AdamDubois/OverClock/Code/Codes_RaspPi/Qt/Interface_9avril/README.md

# Projet Bombe - Code/Code_RaspPi/Qt/Interface_9avril

## Architecture de ce dossier
- OverClockUI : suite des fichiers pour la conception de l'interface.
- OverClockUI.zip : Fichier compressé à mettre sur le Raspberry Pi 4.
