AdamDubois/OverClock/Code/Codes_RaspPi/9Avril/Bouton/README.md

# Projet Bombe - Code/Codes_RaspPi/9Avril/Bouton

## Description

Dossier contenant les codes pour l'énigme des boutons. Il contient les codes pour lire les données des boutons connectés aux ESP32 via I2C et pour envoyer des commandes I2C aux ESP32_DEL pour tester les animations de DEL programmables.

## Architecture de ce dossier

Ce dossier contient les fichiers de code pour l'énigme des boutons, notamment pour les interactions entre le Raspberry Pi et les ESP32 du projet Bombe. Il est organisé de la manière suivante :
- `Config.py` : Fichier de configuration pour les codes de l'énigme des boutons. Il contient les adresses I2C des ESP32 utilisés pour les boutons et les ESP32_DEL, ainsi que les commandes I2C à envoyer pour tester les animations de DEL programmables.
- `EnigmeBouton.py` : Code principal pour l'énigme des boutons. Lit les données du ESP-IO et les traites pour vérifier si elles correspondent à la solution de l'énigme. Affiche les résultats dans la console et envoie des commandes I2C au ESP32_DEL pour tester les animations de DEL programmables en fonction des données reçues.
- `I2C_handler.py` : Fichier de code pour la gestion des communications I2C entre le Raspberry Pi et les ESP32 du projet Bombe. Contient des fonctions pour envoyer des commandes I2C aux ESP32_DEL et pour lire les données des ESP-IO.
- `Log.py` : Fichier de code pour la gestion des logs à afficher dans le terminal pour l'énigme des boutons.
