AdamDubois/OverClock/Code/Codes_RaspPi/Enigmes/1/README.md

# Projet Bombe - Code/Codes_RaspPi/Enigmes/1

## Description

Dossier contenant les codes pour la première énigme du projet Bombe, qui est l'énigme des interrupteurs. Il contient les codes pour lire les données des interrupteurs connectés aux ESP32 via I2C et pour envoyer des commandes I2C aux ESP32_DEL pour tester les animations de DEL programmables.

## Architecture de ce dossier

Ce dossier contient les fichiers de code pour l'énigme des interrupteurs, notamment pour les interactions entre le Raspberry Pi et les ESP32 du projet Bombe. Il est organisé de la manière suivante :
- `Config.py` : Fichier de configuration pour les codes de l'énigme des interrupteurs. Il contient les adresses I2C des ESP32 utilisés pour les interrupteurs et les ESP32_DEL, ainsi que les commandes I2C à envoyer pour tester les animations de DEL programmables.
- `Enigme1.py` : Code principal pour l'énigme des interrupteurs. Lit les données du ESP-IO et les traites pour vérifier si elles correspondent à la solution de l'énigme. Affiche les résultats dans la console et envoie des commandes I2C au ESP32_DEL pour tester les animations de DEL programmables en fonction des données reçues.
- `Enigme1_V2.py` : Version améliorée du code principal pour l'énigme des interrupteurs. Il utilise le fichier `Config.py` pour les adresses I2C et les commandes, et il est structuré de manière plus claire et plus modulaire que la version précédente. Lit les données du ESP-IO et les traites pour vérifier si elles correspondent à la solution de l'énigme. Affiche les résultats dans la console et envoie des commandes I2C au ESP32_DEL pour tester les animations de DEL programmables en fonction des données reçues.
- `Log.py` : Fichier de code pour la gestion des logs à afficher dans le terminal pour l'énigme des interrupteurs.
