AdamDubois/OverClock/Code/Codes_ESP32/0-Desuet/Desuet_ESP32_Feather/Cpp/README.md

# Projet Bombe - Code/Codes_ESP32/0-Desuet/Desuet_ESP32_Feather/Cpp

## Description

Ce dossier contient un projet en C++ avec PlatformIO pour un ESP32-Feather qui est maintenant obsolète et n'est plus utilisé dans le projet Bombe. Le ESP reçoit des données en UART et allume des DELs en fonction de ces données. Ce projet a été remplacé par d'autres projets de code qui utilisent des ESP32-WROOM, mais les fichiers de ce dossier sont conservés à des fins de référence.

## Architecture de ce dossier

- `src/` : Contient tous les fichiers de code qui ont été écrits en C++ pour le projet ESP32-Feather. Ces fichiers ne sont plus utilisés, mais ils sont conservés à des fins de référence.
