AdamDubois/OverClock/Documentation/Référence/fiches techniques/README.md

# Projet Bombe - Documentation/Référence/fiches_techniques
## Description
Ce dossier contient les fiches techniques des composants utilisés dans le projet Bombe. Ces fiches techniques fournissent des informations détaillées sur les caractéristiques, les spécifications et les fonctionnalités de chaque composant, ce qui est essentiel pour la conception et la réalisation du projet.
