AdamDubois/OverClock/Code/Codes_RaspPi/Qt/Interface_9avril/OverClockUI/README.md

# Projet Bombe - Code/Code_RaspPi/Qt/Interface_9avril/OverClockUI

## Architecture de ce dossier
- OverClockUI : suite des fichiers pour la conception de l'interface.
- testJSON.py : permet de tester l’interface en envoyant des données JSON ciblées.
