AdamDubois/OverClock/Code/Codes_RaspPi/Qt/Interface_9avril/OverClockUI/OverClock/OverClockContent/images/rond_code.png

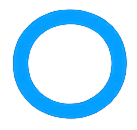
Code/Codes_RaspPi/Qt/Interface_9avril/OverClockUI/OverClock/OverClockContent/images/rond_code.png
