AdamDubois/OverClock/Code/Codes_RaspPi/0-Desuet/Desuet_Codes_Test_RaspPi/img/imgCarrot.jpg

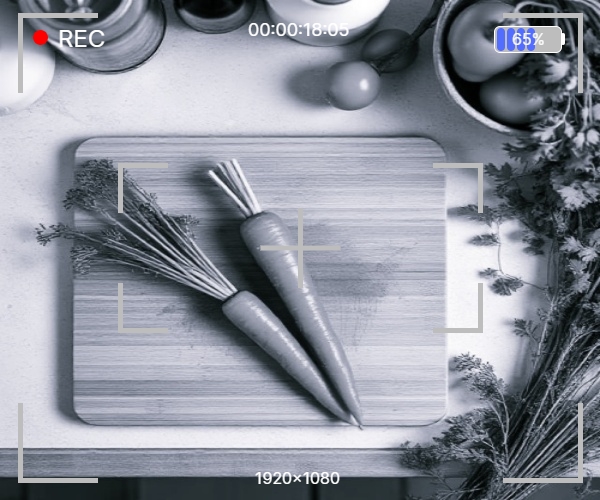
Code/Codes_RaspPi/0-Desuet/Desuet_Codes_Test_RaspPi/img/imgCarrot.jpg
