AdamDubois/OverClock/Code/Codes_ESP32/ESP32_WROOM/0-Desuet/ESP_LED/src/main.cpp

//-----------------------------------------------------------------//
// Includes
#include <config.h> //Fichier de configuration des broches et paramètres (inclut les bibliothèques nécessaires)
#include <Debug_Neo.h> // Bibliothèque de gestion des NeoPixels et des animations
#include <Strips_Neo.h> // Bibliothèque de gestion des NeoPixels et des animations
#include <I2C_Slave.h>
//#################################################################//

//-----------------------------------------------------------------//
#define ETAPES_BLINK 2 // Allumé et éteint
#define ETAPES_RAINBOW 256 // Nombre d'étapes pour l'animation Rainbow
//#################################################################//

//-----------------------------------------------------------------//
// Variables globales
I2C_Slave i2cSlave; // Création d'une instance de la classe I2C_Slave

Debug_Neo DebugNeo; // Création d'une instance de la classe Debug_Neo
Strips_Neo StripsNeo; // Création d'une instance de la classe Strips_Neo

String g_stringOfAllData = "";
bool g_News = false;


String g_stringVerif = "";
int g_intStrip[NB_STRIPS] = {0};
String g_stringCmd[NB_STRIPS] = {""};
String g_stringAnimation[NB_STRIPS] = {""};
int g_intRepetition[NB_STRIPS] = {0};
int g_intNombre[NB_STRIPS] = {0};
int g_intDebut[NB_STRIPS] = {0};
String g_stringCouleur[NB_STRIPS] = {""};
int g_intBrightness[NB_STRIPS] = {0};
int g_delayAnim[NB_STRIPS] = {0};
int g_repetitionAnim[NB_STRIPS] = {0};
int g_etapeAnim[NB_STRIPS] = {0};
//#################################################################//

// put function declarations here:
void initNeoPixels();
void commandeI2C(int howMany);
bool traitementCommande();
uint32_t getColorByName(const String& nom);
void resetVariablesGlobals();
void commandeStat(int str);

void setup() {
  // put your setup code here, to run once:
  Serial.begin(9600);

  StripsNeo.init();
  DebugNeo.init();

  // Initialisation de l'I2C en tant qu'esclave avec l'adresse définie
  Wire.setPins(SDA_PIN, SCL_PIN);
  Wire.begin(SLAVE_ADDR);
  Wire.onReceive(commandeI2C);
  Serial.println("Slave prêt, en attente de requêtes du maître...");
  StripsNeo.allRed(); // Test de tous les NeoPixels avec un effet rouge au démarrage
  delay(1000);
  StripsNeo.allGreen(); // Test de tous les NeoPixels avec un effet vert au démarrage
  delay(1000);
  StripsNeo.allBlue(); // Test de tous les NeoPixels avec un effet bleu au démarrage
  delay(1000);
  StripsNeo.allWhite(); // Test de tous les NeoPixels avec un effet blanc au démarrage
  delay(1000);
  StripsNeo.waterEffect(0, 0xFF0000, 150); // Test de l'effet eau sur le strip 0
}

void loop() {
  // put your main code here, to run repeatedly:
  DebugNeo.waiting();
  if (g_News) // S'il y a des nouvelles données à traiter
  {
    DebugNeo.working();
    Serial.print("Données reçues dans loop: ");
    Serial.println(g_stringOfAllData);

    if(g_stringOfAllData == "") 
    {
        Serial.println("Aucune donnée reçue.");
        DebugNeo.error();
    }
    else if(g_stringOfAllData == "TEST_NEO")
    {
        Serial.println("Lancement du test NeoPixels...");
        //testNeoPixels();
        resetVariablesGlobals(); // Réinitialise les variables après exécution
        DebugNeo.success();
    }
    else
    {
        Serial.println("Parsing du message JSON...");
        if(!traitementCommande())
        {
            Serial.println("Échec du traitement du message UART.");
            resetVariablesGlobals();
            DebugNeo.error();
        }
    }
    g_News = false; // Réinitialise le drapeau
  }
  for (int i = 0; i < NB_STRIPS; i++) {
    if (g_stringCmd[i] == "Stat")
    {
      Serial.println("Commande Stat reçue.");
      commandeStat(i);
      resetVariablesGlobals(); // Réinitialise les variables après exécution
      DebugNeo.success();
    }
    else if (g_stringCmd[i] == "Anim")
    {
      if (g_etapeAnim[i] == 0 && g_repetitionAnim[i] == 0)
      {
          Serial.println("Commande Anim reçue.");
      }
      if (g_delayAnim[i] <= 0)
      {
          //commandeAnim();
          g_delayAnim[i] = 0; // Délai entre les étapes
          DebugNeo.success();
      }
    }
  }

  delay(10); // Petite pause pour calculer les compteurs
  for (int i = 0; i < NB_STRIPS; i++) {
    if (g_delayAnim[i] >= 10)
    {
        g_delayAnim[i] -= 10;
    }
    else 
    {
      g_delayAnim[i] = 0;
    }
  }
}

/*
Brief : Fonction appelée lorsque le maître envoie une commande
*/
void commandeI2C(int howMany) {
  // Lire les données envoyées par le maître
  g_stringOfAllData = "";
  while (Wire.available()) {
    char c = Wire.read();
    g_stringOfAllData += c;
  }
  Serial.println("Données reçues du maître: " + g_stringOfAllData);
  g_News = true;
}

/*
Brief :  Traite le message reçu via UART.
Return : true si le message a été traité avec succès, false sinon.
*/
bool traitementCommande()
{
    JsonDocument doc;

    DeserializationError error = deserializeJson(doc, g_stringOfAllData);

    if (!error) 
    {
        // Récupérer l'indice de strip
        int str = doc["Str"].as<int>();
        if (str < 0 || str >= NB_STRIPS) {
            Serial.println("Numéro de strip invalide !");
            return false; // Index hors limites
        }
        g_intStrip[0] = str;

        // Extraction des valeurs pour le strip str
        g_stringVerif         = doc["V"]          | "";
        g_stringCmd[str]      = doc["Cmd"]        | "";
        g_stringAnimation[str]= doc["Anim"]       | "";
        g_intNombre[str]      = doc["Nbr"].as<int>();
        g_intDebut[str]       = doc["Deb"].as<int>();
        g_stringCouleur[str]  = doc["Coul"]       | "";
        g_intRepetition[str]  = doc["Rep"].as<int>();
        g_intBrightness[str]  = doc["Br"].as<int>();
        g_delayAnim[str]      = doc["Wait"].as<int>();
        g_repetitionAnim[str] = doc["Rep"].as<int>();
        // Remplir ou remettre à zéro des champs d'animation selon besoin

        if (g_intBrightness[str] < 0)
        {
            g_intBrightness[str] = 0;
            // Serial.println("Brightness trop bas, réglé à 0.");
        }
        else if (g_intBrightness[str] > 255)
        {
            g_intBrightness[str] = 255;
            // Serial.println("Brightness trop haut, réglé à 255.");
        }   

        // Serial.println("Message JSON parsé avec succès:");
        // Serial.print("Strip: "); Serial.println(str);
        // Serial.print("Verif: "); Serial.println(g_stringVerif);
        // Serial.print("Cmd: "); Serial.println(g_stringCmd[str]);
        // Serial.print("Animation: "); Serial.println(g_stringAnimation[str]);
        // Serial.print("Nombre: "); Serial.println(g_intNombre[str]);
        // Serial.print("Debut: "); Serial.println(g_intDebut[str]);
        // Serial.print("Couleur: "); Serial.println(g_stringCouleur[str]);
        // Serial.print("Repetition: "); Serial.println(g_intRepetition[str]);
        // Serial.print("Brightness: "); Serial.println(g_intBrightness[str]);
        // Serial.print("Delay: "); Serial.println(g_delayAnim[str]);
    } 
    else 
    {
        Serial.print("Erreur parser JSON : ");
        Serial.println(error.c_str());
        return false; // Échec du parsing
    }
    
    return true; // Succès du traitement
}

/*
Brief :  Récupère le code couleur NeoPixel correspondant au nom de couleur donné.
*/
uint32_t getColorByName(const String& nom) {
  for (int i = 0; i < NB_COLORS; i++) {
    if (nom.equalsIgnoreCase(color_table[i].name)) {
      return color_table[i].value;
    }
  }
  // Couleur inconnue: retour noir/off
  return Adafruit_NeoPixel::Color(0, 0, 0);
}

/*
Brief :  Réinitialise les variables globales liées au message UART.
*/
void resetVariablesGlobals()
{
    g_stringVerif = "";
    for (int i = 0; i < NB_STRIPS; i++) {
        g_intStrip[i] = 0;
        g_stringCmd[i] = "";
        g_stringAnimation[i] = "";
        g_intRepetition[i] = 0;
        g_intNombre[i] = 0;
        g_intDebut[i] = 0;
        g_stringCouleur[i] = "";
        g_intBrightness[i] = 0;
        g_delayAnim[i] = 0;
        g_repetitionAnim[i] = 0;
        g_etapeAnim[i] = 0;
    }
}

/*
Brief :  Exécute la commande "Stat".
*/
void commandeStat(int str)
{
      StripsNeo.strips[str].setBrightness(g_intBrightness[str]);
      uint32_t color = getColorByName(g_stringCouleur[str]);
      StripsNeo.strips[str].fill(color);
      StripsNeo.strips[str].show();
}
