AdamDubois/OverClock/Code/Codes_RaspPi/0-Desuet/Desuet_Jeu1/Jeu.py

#!/usr/bin/env python
#coding: utf-8
"""
Fichier : Proto.py
Description: Programme principal pour gérer les interactions entre les composants matériels via GPIO, I2C, SPI, UART et UDP.
"""
__author__ = "Adam Dubois et Jérémy Breault"
__version__ = "1.0.1"
__date__ = "2026-01-09"
__maintainer__ = "Adam Dubois"
__email__ = "adamdubois19@hotmail.com"
__status__ = "Production"


import time
import RPi.GPIO as GPIO
from lib.Class_UDP import UDPListener
from lib.Class_EcranI2C import EcranI2C
from lib.Class_RFID import RFIDReader
from lib.Class_UART import UART
from lib.Class_Bouton import Bouton
from lib.Class_KeyPad import KeyPad
from lib.Log import logger

code_keypad = "1234"  # Code d'accès pour le KeyPad

#-----------------------------------------------#
# Configuration initiale du programme           #
#-----------------------------------------------#
boutons = Bouton()

#-----------------------------------------------#
# Configuration du KeyPad                       #
#-----------------------------------------------#
keypad = KeyPad()

#-----------------------------------------------#
# Initialisation de l'écran I2C                 #
#-----------------------------------------------#
# Créer une instance de l'écran I2C
ecran = EcranI2C()

#-----------------------------------------------#
# Initialisation du RFID                        #
#-----------------------------------------------#
rfid_reader = RFIDReader()

#-----------------------------------------------#
# Initialisation du listener UDP                #
#-----------------------------------------------#
# Démarrer le listener UDP
listener = UDPListener()

#-----------------------------------------------#
# Initialisation du module UART                 #
#-----------------------------------------------#
uart_handler = UART()

#-----------------------------------------------#
# Boucle principale du programme                #
#-----------------------------------------------#
logger.info("[Proto] Programme principal démarré. Le serveur UDP écoute en arrière-plan.")
logger.warning("[Proto] Programme principal démarré. Appuyez sur Ctrl+C pour arrêter.")
ecran.afficher_texte("Programme démarré", position=(0, (ecran.hauteur/2)))
time.sleep(2)
ecran.effacer_ecran()

try:
    ecran.afficher_texte("Choisir un mode :\n1 : Code KeyPad\n2 : Code UDP\n3 : Code RFID", position=(0, 0))
    while True:
        time.sleep(0.1)  # Petite pause pour éviter une boucle trop rapide

        if keypad.key_pressed:
            match keypad.key_pressed:
                case '1':
                    ecran.effacer_ecran()
                    ecran.afficher_texte("Mode KeyPad\nsélectionné", position=(0, 16))
                    logger.info("[Proto] Mode KeyPad sélectionné.")
                    uart_handler.send_message(("{C:\"UART_Neo\",V:\"\",Cmd:\"Stat\",Nbr:75,Deb:0,Coul:\"RED\",Br:100}" + "\n"))
                    keypad.key_pressed = None  # Réinitialiser la touche pressée
                    index = 0
                    while True:
                        time.sleep(0.1)
                        if keypad.key_pressed:
                            if keypad.key_pressed == '#':
                                break
                            else:
                                if keypad.key_pressed == code_keypad[index]:
                                    index += 1
                                    ecran.afficher_texte("*" * index, position=(0, 32))
                                    uart_handler.send_message(("{C:\"UART_Neo\",V:\"\",Cmd:\"Stat\",Nbr:19,Deb:" + str((index-1)*19) + ",Coul:\"GREEN\",Br:100}" + "\n"))
                                    keypad.key_pressed = None  # Réinitialiser la touche pressée
                                    if index == len(code_keypad):
                                        ecran.effacer_ecran()
                                        ecran.afficher_texte("Code correct!\nAccès autorisé.", position=(0, 16))
                                        logger.info("[Proto] Code KeyPad correct. Accès autorisé.")
                                        uart_handler.send_message(("{C:\"UART_Neo\",V:\"\",Cmd:\"Anim\",Nbr:75,Deb:0,Coul:\"GREEN\",Br:100,Anim:\"Rainbow\",Rep:10000}" + "\n"))
                                        time.sleep(5)
                                        keypad.key_pressed = "#"
                                        break
                                else:
                                    ecran.effacer_ecran()
                                    ecran.afficher_texte("Code incorrect!\nRéessayez.", position=(0, 16))
                                    logger.warning("[Proto] Code KeyPad incorrect.")
                                    uart_handler.send_message(("{C:\"UART_Neo\",V:\"\",Cmd:\"Stat\",Nbr:75,Deb:0,Coul:\"RED\",Br:100}" + "\n"))
                                    time.sleep(2)
                                    ecran.effacer_ecran()
                                    ecran.afficher_texte("Mode KeyPad\nsélectionné", position=(0, 16))
                                    index = 0
                                    keypad.key_pressed = None
                case '2':
                    ecran.effacer_ecran()
                    ecran.afficher_texte("Mode UDP\nsélectionné", position=(0, 16))
                    logger.info("[Proto] Mode UDP sélectionné.")
                    uart_handler.send_message(("{C:\"UART_Neo\",V:\"\",Cmd:\"Stat\",Nbr:75,Deb:0,Coul:\"RED\",Br:100}" + "\n"))
                    keypad.key_pressed = None  # Réinitialiser la touche pressée
                case '3':
                    ecran.effacer_ecran()
                    ecran.afficher_texte("Mode RFID\nsélectionné", position=(0, 16))
                    logger.info("[Proto] Mode RFID sélectionné.")
                    uart_handler.send_message(("{C:\"UART_Neo\",V:\"\",Cmd:\"Stat\",Nbr:75,Deb:0,Coul:\"RED\",Br:100}" + "\n"))
                    keypad.key_pressed = None  # Réinitialiser la touche pressée
                case '#':
                    ecran.afficher_texte("Choisir un mode :\n1 : Code KeyPad\n2 : Code UDP\n3 : Code RFID", position=(0, 0))
                    uart_handler.send_message(("{C:\"UART_Neo\",V:\"\",Cmd:\"Stat\",Nbr:75,Deb:0,Coul:\"BLUE\",Br:100}" + "\n"))
                    keypad.key_pressed = None  # Réinitialiser la touche pressée
                case _:
                    keypad.key_pressed = None  # Réinitialiser la touche pressée si non gérée

#-----------------------------------------------#
# Arrêt propre du programme                     #
#-----------------------------------------------#
# Gérer l'arrêt propre du programme Ctrl+C
except KeyboardInterrupt:
    logger.warning("[Proto] Arrêt demandé par l'utilisateur (Ctrl+C).")

# Dans tous les cas, s'assurer que tout est arrêté correctement
finally:
    logger.warning("[Proto] Arrêt du programme...")
    listener.stop() # Arrête le listener UDP
    listener.join(timeout=2) # Attend la fin du thread UDP
    uart_handler.close() # Ferme le port UART
    boutons.stop() # Arrête le thread des boutons
    boutons.join(timeout=2) # Attend la fin du thread des boutons
    rfid_reader.stop() # Arrête le thread RFID
    rfid_reader.join(timeout=2) # Attend la fin du thread RFID
    ecran.effacer_ecran() # Efface l'écran avant de quitter
    GPIO.cleanup() # Nettoie les configurations GPIO
    logger.warning("[Proto] Programme terminé.")
