AdamDubois/OverClock/Code/Codes_RaspPi/0-Desuet/Desuet_Codes_Test_RaspPi/protoUI.py

<<<<<<< Updated upstream:Code/Code_Test/protoUI.py
#!/usr/bin/env python
#coding: utf-8
"""
Fichier : protoUI.py
Description: Code de test pour l'interface utilisateur PyQt5.
    - Crée une fenêtre principale avec un style sombre.
    - Affiche un titre et une console de style "hacker" avec des commandes qui défilent.
    - Intègre une section pour afficher des images de caméra qui changent périodiquement.
"""
__author__ = "Adam Dubois et Jérémy Breault"
__version__ = "1.0.1"
__date__ = "2025-12-05"
__maintainer__ = "Adam Dubois"
__email__ = "adamdubois19@hotmail.com"
__status__ = "Production"


# =====================================================#
#                        Imports                       #
# =====================================================#
import sys
import random
import time
from PyQt5.QtWidgets import QApplication, QMainWindow, QLabel, QFrame, QTextEdit
from PyQt5.QtCore import Qt, QTimer
from PyQt5.QtGui import QFont

import os
os.environ['DISPLAY'] = ':0'
  

# =====================================================#
#                    Classe Principale                 #
# =====================================================#

titre_Du_Projet = "Projet InXtremis"#Titre du projet

# =================== Liste image Camera ==============#
IMAGE_CAMERA = [
    '/home/admin/Documents/Projet_InXtremis/code/img/imgFraise.jpg',  #0
    '/home/admin/Documents/Projet_InXtremis/code/img/imgAvocado.jpg', #1
    '/home/admin/Documents/Projet_InXtremis/code/img/imgCarrot.jpg',  #2
    '/home/admin/Documents/Projet_InXtremis/code/img/imgKiwi.jpg',    #3
    '/home/admin/Documents/Projet_InXtremis/code/img/imgBanane.jpg',  #4
    '/home/admin/Documents/Projet_InXtremis/code/img/imgPiment.jpg',  #5
    '/home/admin/Documents/Projet_InXtremis/code/img/imgTomate.jpg',  #6
    '/home/admin/Documents/Projet_InXtremis/code/img/NoSignal.jpg'    #7
]

ORDRE_CAMERA = [2,6,4,1,5,3,0] 


#=================== Liste de commande de style "hacker" ===================#
COMMANDS = [
    "init_link -addr 10.0.0.19 --sync",
    "auth: token=0x4f2a9c... validated",
    "scan_ports --range 1-65535 --fast",
    "decrypt --keyfile /tmp/key.bin",
    "payload_upload --target 192.168.0.42",
    "grep 'ERROR'/CODE = 3478 /var/log/syslog | tail -n 50",
    "mount -o remount,rw /",
    "ssh root@198.51.100.10 -p 2222",
    "curl -s http://mirror/pack | tar -xzf -",
    "db.query('SELECT * FROM users WHERE active=1')",
    "watchdog: heartbeat OK",
    "compile --optimize -j8 module_core",
    "inject --mem 0x7ffdf000 --size 0x400",
    "ifconfig eth0 down && ifconfig eth0 up",
    "rm -rf /tmp/.cache && sync",
    "openssl s_client -connect example.com:443",
    "echo 1 > /proc/sys/net/ipv4/ip_forward",
    "nmap -sS -Pn -T4 10.0.0.0/24",
]

class MainWindow(QMainWindow):
    def __init__(self):
        super().__init__()
        dark_style = """
        QMainWindow {
            background-color: #121212;
            color: #FFFFFF;
        }
        """
        self.setStyleSheet(dark_style)
        self.setWindowTitle("InXtremis") #titre de la fenetre
        self.initUI()
        
    def initUI(self):
        label = QLabel(titre_Du_Projet, self)
        label.setFont(QFont("Forte", 30))
        label.setGeometry(50, 50, 500, 100)
        label.setStyleSheet("color: green;")

        # Créer un frame pour la console hacker
        console_frame = QFrame(self)
        console_frame.setGeometry(30, 500, 1200, 500)
        console_frame.setStyleSheet("""
            QFrame {
                background-color: rgba(5,5,5,0.9); 
                border: 2px solid #00ff00;
                border-radius: 8px;
                padding: 8px;
            }
        """)

        # Titre de la console
        label_console = QLabel("=== CONSOLE SYSTÈME ===", self)
        label_console.setGeometry(30, 470, 400, 30)
        label_console.setStyleSheet("""
            color: #00ff00;
            font-weight: bold;
            text-align: center;
        """)

        # Zone de texte pour afficher les commandes qui défilent
        self.console_text = QTextEdit(console_frame)
        self.console_text.setGeometry(10, 10, 1180, 480)
        self.console_text.setReadOnly(True)  # Lecture seule
        
        # Enlever les barres de défilement
        self.console_text.setVerticalScrollBarPolicy(Qt.ScrollBarAlwaysOff)
        self.console_text.setHorizontalScrollBarPolicy(Qt.ScrollBarAlwaysOff)
        
        self.console_text.setStyleSheet("""
            QTextEdit {
                background-color: rgba(0,0,0,0.9);
                color: #00ff00;
                font-family: 'Courier New', monospace;
                font-size: 20px;
                border: none;
                padding: 5px;
            }
        """)

        # Variables pour le défilement
        self.command_index = 0
        
        # Variables pour la rotation des images de caméra
        self.camera_index = 0
        
        # Démarrer le défilement automatique
        self.demarrer_defilement()


        #Affichage de la console retour Camera
        self.camera_frame = QFrame(self)
        self.camera_frame.setGeometry(1300, 500, 600, 500)
        
        # Démarrer avec la première image de l'ordre
        self.changer_image_camera()
        
        # Démarrer la rotation des images de caméra
        self.demarrer_rotation_camera()
        self.camera_text = QTextEdit(self.camera_frame)
        self.camera_text.setGeometry(10, 10, 580, 480)
        self.camera_text.setReadOnly(True)  # Lecture seule
        self.camera_text.setStyleSheet("""
            QTextEdit {
                background-color: rgba(0,0,0,0.9);
                color: #00ff00;
                font-family: 'Courier New', monospace;
                font-size: 20px;
                border: none;
                padding: 5px;
            }
        """)


    def demarrer_defilement(self):
        """Démarre le défilement des commandes avec délai aléatoire"""
        # Créer et démarrer le timer - pas de message d'initialisation
        self.timer = QTimer()
        self.timer.timeout.connect(self.nouvelle_commande)
        # Délai aléatoire entre 1 et 4 secondes pour commencer
        delai_initial = random.randint(500, 3000)
        self.timer.start(delai_initial)
        
    def nouvelle_commande(self):
        commande = COMMANDS[self.command_index]
        self.command_index += 1
        
        if self.command_index >= len(COMMANDS):
            self.command_index = 0
        
        timestamp = time.strftime("%H:%M:%S")
        self.console_text.append(f"[{timestamp}] root@inxtremis:~$ {commande}")
        
        # Scroll automatique vers le bas
        scrollbar = self.console_text.verticalScrollBar()
        scrollbar.setValue(scrollbar.maximum())
        
        delai_suivant = random.randint(1000, 3000)
        self.timer.start(delai_suivant)

    def demarrer_rotation_camera(self):
        """Démarre la rotation des images de caméra selon l'ordre défini"""
        self.timer_camera = QTimer()
        self.timer_camera.timeout.connect(self.changer_image_camera_suivante)
        self.timer_camera.start(3000)  # Change toutes les 3 secondes
    

    def changer_image_camera(self):
        """Change l'image de fond de la caméra selon l'index actuel"""
        # Récupérer l'index de l'image selon l'ordre défini
        image_index = ORDRE_CAMERA[self.camera_index]
        image_choisie = IMAGE_CAMERA[image_index]
        
        self.camera_frame.setStyleSheet(f"""
            QFrame {{
                background-image: url('{image_choisie}');
                background-repeat: no-repeat;
                background-position: center;
                background-size: cover; 
                border: 2px solid #00ff00;
                border-radius: 8px;
                padding: 8px;
            }}
        """)
    
    #Fonction pour changer d'image
    def changer_image_camera_suivante(self):
        """Passe à l'image suivante dans l'ordre défini avec possibilité d'afficher NoSignal aléatoirement"""
        
        # 20% de chance d'afficher l'image NoSignal (index 7) au lieu de l'ordre normal
        if random.randint(1, 100) <= 20:  # 20% de chance
            self.afficher_image_nosignal()
        else:
            # Affichage normal selon l'ordre défini
            self.camera_index += 1
            
            # Recommencer au début quand on atteint la fin de l'ordre
            if self.camera_index >= len(ORDRE_CAMERA):
                self.camera_index = 0
                
            self.changer_image_camera()
    
    #Fonction pour l'imgae avec pas de signal
    def afficher_image_nosignal(self):
        """Affiche temporairement l'image NoSignal"""
        image_nosignal = IMAGE_CAMERA[7]  # Index 7 = NoSignal.jpg
        
        self.camera_frame.setStyleSheet(f"""
            QFrame {{
                background-image: url('{image_nosignal}');
                background-repeat: no-repeat;
                background-position: center;
                background-size: cover; 
                border: 2px solid #00ff00;
                border-radius: 8px;
                padding: 8px;
            }}
        """)


def main():
    app = QApplication(sys.argv) 
    window = MainWindow() 
    
    # Pour prendre TOUT l'écran et cacher la barre de tâches du système
    window.showFullScreen()
   
    
    sys.exit(app.exec_())


if __name__ == "__main__":
    main()
    
=======
#!/usr/bin/env python
#coding: utf-8
"""
Fichier : protoUI.py
Description: Code de test pour l'interface utilisateur PyQt5.
    - Crée une fenêtre principale avec un style sombre.
    - Affiche un titre et une console de style "hacker" avec des commandes qui défilent.
    - Intègre une section pour afficher des images de caméra qui changent périodiquement.
"""
__author__ = "Adam Dubois et Jérémy Breault"
__version__ = "1.0.1"
__date__ = "2025-12-05"
__maintainer__ = "Adam Dubois"
__email__ = "adamdubois19@hotmail.com"
__status__ = "Production"


# =====================================================#
#                        Imports                       #
# =====================================================#
import sys
import random
import time
from PyQt5.QtWidgets import QApplication, QMainWindow, QLabel, QFrame, QTextEdit
from PyQt5.QtCore import Qt, QTimer
from PyQt5.QtGui import QFont
  

# =====================================================#
#                    Classe Principale                 #
# =====================================================#

titre_Du_Projet = "Projet InXtremis"#Titre du projet

# =================== Liste image Camera ==============#
IMAGE_CAMERA = [
    'c:/VSCodeProject/Project_AI/Bombe/img/imgFraise.jpg',  #0
    'c:/VSCodeProject/Project_AI/Bombe/img/imgAvocado.jpg', #1
    'c:/VSCodeProject/Project_AI/Bombe/img/imgCarrot.jpg',  #2
    'c:/VSCodeProject/Project_AI/Bombe/img/imgKiwi.jpg',    #3
    'c:/VSCodeProject/Project_AI/Bombe/img/imgBanane.jpg',  #4
    'c:/VSCodeProject/Project_AI/Bombe/img/imgPiment.jpg',  #5
    'c:/VSCodeProject/Project_AI/Bombe/img/imgTomate.jpg',  #6
    'c:/VSCodeProject/Project_AI/Bombe/img/NoSignal.jpg'    #7
]

ORDRE_CAMERA = [2,6,4,1,5,3,0] 


#=================== Liste de commande de style "hacker" ===================#
COMMANDS = [
    "init_link -addr 10.0.0.19 --sync",
    "auth: token=0x4f2a9c... validated",
    "scan_ports --range 1-65535 --fast",
    "decrypt --keyfile /tmp/key.bin",
    "payload_upload --target 192.168.0.42",
    "grep 'ERROR'/CODE = 3478 /var/log/syslog | tail -n 50",
    "mount -o remount,rw /",
    "ssh root@198.51.100.10 -p 2222",
    "curl -s http://mirror/pack | tar -xzf -",
    "db.query('SELECT * FROM users WHERE active=1')",
    "watchdog: heartbeat OK",
    "compile --optimize -j8 module_core",
    "inject --mem 0x7ffdf000 --size 0x400",
    "ifconfig eth0 down && ifconfig eth0 up",
    "rm -rf /tmp/.cache && sync",
    "openssl s_client -connect example.com:443",
    "echo 1 > /proc/sys/net/ipv4/ip_forward",
    "nmap -sS -Pn -T4 10.0.0.0/24",
]

class MainWindow(QMainWindow):
    def __init__(self):
        super().__init__()
        dark_style = """
        QMainWindow {
            background-color: #121212;
            color: #FFFFFF;
        }
        """
        self.setStyleSheet(dark_style)
        self.setWindowTitle("InXtremis") #titre de la fenetre
        self.initUI()
        
    def initUI(self):
        label = QLabel(titre_Du_Projet, self)
        label.setFont(QFont("Forte", 30))
        label.setGeometry(50, 50, 500, 100)
        label.setStyleSheet("color: green;")

        # Créer un frame pour la console hacker
        console_frame = QFrame(self)
        console_frame.setGeometry(30, 500, 1200, 500)
        console_frame.setStyleSheet("""
            QFrame {
                background-color: rgba(5,5,5,0.9); 
                border: 2px solid #00ff00;
                border-radius: 8px;
                padding: 8px;
            }
        """)

        # Titre de la console
        label_console = QLabel("=== CONSOLE SYSTÈME ===", self)
        label_console.setGeometry(30, 470, 400, 30)
        label_console.setStyleSheet("""
            color: #00ff00;
            font-weight: bold;
            text-align: center;
        """)

        # Zone de texte pour afficher les commandes qui défilent
        self.console_text = QTextEdit(console_frame)
        self.console_text.setGeometry(10, 10, 1180, 480)
        self.console_text.setReadOnly(True)  # Lecture seule
        
        # Enlever les barres de défilement
        self.console_text.setVerticalScrollBarPolicy(Qt.ScrollBarAlwaysOff)
        self.console_text.setHorizontalScrollBarPolicy(Qt.ScrollBarAlwaysOff)
        
        self.console_text.setStyleSheet("""
            QTextEdit {
                background-color: rgba(0,0,0,0.9);
                color: #00ff00;
                font-family: 'Courier New', monospace;
                font-size: 20px;
                border: none;
                padding: 5px;
            }
        """)

        # Variables pour le défilement
        self.command_index = 0
        
        # Variables pour la rotation des images de caméra
        self.camera_index = 0
        
        # Démarrer le défilement automatique
        self.demarrer_defilement()


        #Affichage de la console retour Camera
        self.camera_frame = QFrame(self)
        self.camera_frame.setGeometry(1300, 500, 600, 500)
        
        # Démarrer avec la première image de l'ordre
        self.changer_image_camera()
        
        # Démarrer la rotation des images de caméra
        self.demarrer_rotation_camera()
        self.camera_text = QTextEdit(self.camera_frame)
        self.camera_text.setGeometry(10, 10, 580, 480)
        self.camera_text.setReadOnly(True)  # Lecture seule
        self.camera_text.setStyleSheet("""
            QTextEdit {
                background-color: rgba(0,0,0,0.9);
                color: #00ff00;
                font-family: 'Courier New', monospace;
                font-size: 20px;
                border: none;
                padding: 5px;
            }
        """)


    def demarrer_defilement(self):
        """Démarre le défilement des commandes avec délai aléatoire"""
        # Créer et démarrer le timer - pas de message d'initialisation
        self.timer = QTimer()
        self.timer.timeout.connect(self.nouvelle_commande)
        # Délai aléatoire entre 1 et 4 secondes pour commencer
        delai_initial = random.randint(500, 3000)
        self.timer.start(delai_initial)
        
    def nouvelle_commande(self):
        commande = COMMANDS[self.command_index]
        self.command_index += 1
        
        if self.command_index >= len(COMMANDS):
            self.command_index = 0
        
        timestamp = time.strftime("%H:%M:%S")
        self.console_text.append(f"[{timestamp}] root@inxtremis:~$ {commande}")
        
        # Scroll automatique vers le bas
        scrollbar = self.console_text.verticalScrollBar()
        scrollbar.setValue(scrollbar.maximum())
        
        delai_suivant = random.randint(1000, 3000)
        self.timer.start(delai_suivant)

    def demarrer_rotation_camera(self):
        """Démarre la rotation des images de caméra selon l'ordre défini"""
        self.timer_camera = QTimer()
        self.timer_camera.timeout.connect(self.changer_image_camera_suivante)
        self.timer_camera.start(3000)  # Change toutes les 3 secondes
    

    def changer_image_camera(self):
        """Change l'image de fond de la caméra selon l'index actuel"""
        # Récupérer l'index de l'image selon l'ordre défini
        image_index = ORDRE_CAMERA[self.camera_index]
        image_choisie = IMAGE_CAMERA[image_index]
        
        self.camera_frame.setStyleSheet(f"""
            QFrame {{
                background-image: url('{image_choisie}');
                background-repeat: no-repeat;
                background-position: center;
                border: 2px solid #00ff00;
                border-radius: 8px;
                padding: 8px;
            }}
        """)
    
    #Fonction pour changer d'image
    def changer_image_camera_suivante(self):
        """Passe à l'image suivante dans l'ordre défini avec possibilité d'afficher NoSignal aléatoirement"""
        
        # 20% de chance d'afficher l'image NoSignal (index 7) au lieu de l'ordre normal
        if random.randint(1, 100) <= 20:  # 20% de chance
            self.afficher_image_nosignal()
        else:
            # Affichage normal selon l'ordre défini
            self.camera_index += 1
            
            # Recommencer au début quand on atteint la fin de l'ordre
            if self.camera_index >= len(ORDRE_CAMERA):
                self.camera_index = 0
                
            self.changer_image_camera()
    
    #Fonction pour l'imgae avec pas de signal
    def afficher_image_nosignal(self):
        """Affiche temporairement l'image NoSignal"""
        image_nosignal = IMAGE_CAMERA[7]  # Index 7 = NoSignal.jpg
        
        self.camera_frame.setStyleSheet(f"""
            QFrame {{
                background-image: url('{image_nosignal}');
                background-repeat: no-repeat;
                background-position: center;
                border: 2px solid #00ff00;
                border-radius: 8px;
                padding: 8px;
            }}
        """)


def main():
    app = QApplication(sys.argv) 
    window = MainWindow() 
    
    # Pour prendre TOUT l'écran et cacher la barre de tâches du système
    window.showFullScreen()
   
    
    sys.exit(app.exec_())


if __name__ == "__main__":
    main()
    
>>>>>>> Stashed changes:Code_Test/protoUI.py
