AdamDubois/OverClock/Code/Codes_ESP32/ESP32_WROOM/1-Codes_Tests/Tests_Animations/include/HelpRain.h

#ifndef HELPRRAIN_H
#define HELPRRAIN_H

#include "config.h"

#define HELP_ANIMATION_FRAME_COUNT 52

static const uint32_t help_animation_data[HELP_ANIMATION_FRAME_COUNT][256] = {
{
0xffff8900, 0xfffff900, 0xff94ff00, 0xff02ff00, 0xff00ff9c, 0xff00c5ff, 0xff006bff, 0xff0000ff, 0xff006bff, 0xff00c5ff, 0xff00ff9c, 0xff02ff00, 0xff94ff00, 0xfffff900, 0xffff8900, 0xffff0200, 0xffff00a7, 0xfffd00ff, 0xff4900ff, 0xff0000ff, 0xff4900ff, 0xfffd00ff, 0xffff00a7, 0xffff0200, 0xffff8900, 0xfffff900, 0xff94ff00, 0xff02ff00, 0xff00ff9c, 0xff00c5ff, 0xff006bff, 0xff0000ff, 
0x00000000, 0x00000000, 0x00000000, 0x00000000, 0x00000000, 0x00000000, 0x00000000, 0x00000000, 0x00000000, 0x00000000, 0x00000000, 0x00000000, 0x00000000, 0x00000000, 0x00000000, 0x00000000, 0x00000000, 0x00000000, 0x00000000, 0x00000000, 0x00000000, 0x00000000, 0x00000000, 0x00000000, 0x00000000, 0x00000000, 0x00000000, 0x00000000, 0x00000000, 0x00000000, 0x00000000, 0x00000000, 
0x00000000, 0x00000000, 0x00000000, 0x00000000, 0x00000000, 0x00000000, 0x00000000, 0x00000000, 0x00000000, 0x00000000, 0x00000000, 0x00000000, 0x00000000, 0x00000000, 0x00000000, 0x00000000, 0x00000000, 0x00000000, 0x00000000, 0x00000000, 0x00000000, 0x00000000, 0x00000000, 0x00000000, 0x00000000, 0x00000000, 0x00000000, 0x00000000, 0x00000000, 0x00000000, 0x00000000, 0x00000000, 
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
0x00000000, 0x00000000, 0x00000000, 0x00000000, 0x00000000, 0x00000000, 0x00000000, 0x00000000, 0x00000000, 0x00000000, 0x00000000, 0x00000000, 0x00000000, 0x00000000, 0x00000000, 0x00000000, 0x00000000, 0x00000000, 0x00000000, 0xff0000ff, 0xff0000ff, 0xff0000ff, 0xff0000ff, 0x00000000, 0xff0000ff, 0xff0000ff, 0xff0000ff, 0xff0000ff, 0x00000000, 0xff0000ff, 0x00000000, 0x00000000, 
0x00000000, 0x00000000, 0x00000000, 0x00000000, 0x00000000, 0x00000000, 0x00000000, 0x00000000, 0x00000000, 0x00000000, 0x00000000, 0x00000000, 0x00000000, 0x00000000, 0x00000000, 0x00000000, 0x00000000, 0x00000000, 0x00000000, 0xff0000ff, 0x00000000, 0x00000000, 0xff0000ff, 0x00000000, 0xff0000ff, 0x00000000, 0x00000000, 0x00000000, 0x00000000, 0xff0000ff, 0x00000000, 0x00000000,
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
